kattemjau/MountainX-remote/Images/image (1).png

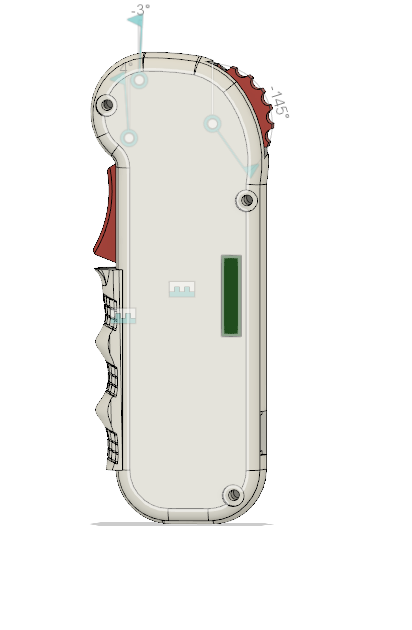
Images/image (1).png
