kattemjau/MountainX-remote/Images/image.png

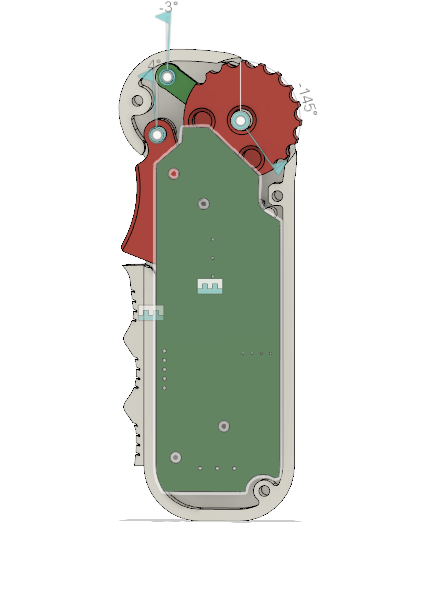
Images/image.png
